JakubJaszczur/Epaper-Weather-Station-Receiver/src/myFont.h

// Created by http://oleddisplay.squix.ch/ Consider a donation
// In case of problems make sure that you are using the font file with the correct version!
const uint8_t SansSerif_bold_50Bitmaps[] PROGMEM = {

	// Bitmap Data:
	0x00, // ' '
	0xFF,0xBF,0xEF,0xFB,0xFE,0xFF,0xBF,0xEF,0xFB,0xFE,0xFF,0xBF,0xEF,0xFB,0xFE,0xFF,0xBF,0xEF,0xFB,0xFE,0xFF,0xBF,0xE7,0xF1,0xFC,0x7F,0x1F,0xC7,0xF1,0xFC,0x00,0x00,0x00,0x03,0xFE,0xFF,0xBF,0xEF,0xFB,0xFE,0xFF,0xBF,0xEF,0xFB,0xFE, // '!'
	0xFC,0x1F,0xBF,0x07,0xEF,0xC1,0xFB,0xF0,0x7E,0xFC,0x1F,0xBF,0x07,0xEF,0xC1,0xFB,0xF0,0x7E,0xFC,0x1F,0xBF,0x07,0xEF,0xC1,0xFB,0xF0,0x7E,0xFC,0x1F,0xBF,0x07,0xE0, // '"'
	0x00,0x07,0xE0,0x7E,0x00,0x00,0x7C,0x07,0xC0,0x00,0x07,0xC0,0x7C,0x00,0x00,0xFC,0x0F,0xC0,0x00,0x0F,0xC0,0xF8,0x00,0x00,0xF8,0x0F,0x80,0x00,0x0F,0x80,0xF8,0x00,0x01,0xF8,0x1F,0x80,0x00,0x1F,0x81,0xF0,0x01,0xFF,0xFF,0xFF,0xFE,0x1F,0xFF,0xFF,0xFF,0xE1,0xFF,0xFF,0xFF,0xFE,0x1F,0xFF,0xFF,0xFF,0xE1,0xFF,0xFF,0xFF,0xFE,0x00,0x3E,0x07,0xE0,0x00,0x07,0xE0,0x7E,0x00,0x00,0x7E,0x07,0xC0,0x00,0x07,0xC0,0x7C,0x00,0x00,0x7C,0x0F,0xC0,0x00,0x0F,0xC0,0xFC,0x00,0x00,0xFC,0x0F,0x80,0x0F,0xFF,0xFF,0xFF,0xF0,0xFF,0xFF,0xFF,0xFF,0x0F,0xFF,0xFF,0xFF,0xF0,0xFF,0xFF,0xFF,0xFF,0x0F,0xFF,0xFF,0xFF,0xF0,0x01,0xF0,0x1F,0x00,0x00,0x3F,0x03,0xF0,0x00,0x03,0xF0,0x3E,0x00,0x00,0x3E,0x03,0xE0,0x00,0x03,0xE0,0x3E,0x00,0x00,0x3E,0x07,0xE0,0x00,0x07,0xE0,0x7E,0x00,0x00,0x7C,0x07,0xC0,0x00,0x07,0xC0,0x7C,0x00,0x00,0x7C,0x0F,0xC0,0x00, // '#'
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
};
const GFXglyph SansSerif_bold_50Glyphs[] PROGMEM = {
// bitmapOffset, width, height, xAdvance, xOffset, yOffset
	  {     0,   1,   1,  18,    0,    0 }, // ' '
	  {     1,  10,  36,  24,    7,  -36 }, // '!'
	  {    46,  18,  14,  27,    5,  -36 }, // '"'
	  {    78,  36,  36,  43,    3,  -36 }, // '#'
	  {   240,  29,  45,  36,    3,  -38 }, // '$'
	  {   404,  48,  38,  51,    2,  -37 }, // '%'
	  {   632,  40,  38,  45,    2,  -37 }, // '&'
	  {   822,   7,  14,  16,    5,  -36 }, // '''
	  {   835,  15,  45,  24,    4,  -38 }, // '('
	  {   920,  15,  45,  24,    4,  -38 }, // ')'
	  {  1005,  25,  23,  27,    1,  -37 }, // '*'
	  {  1077,  33,  32,  43,    5,  -32 }, // '+'
	  {  1209,  12,  17,  20,    3,   -9 }, // ','
	  {  1235,  16,   7,  22,    3,  -18 }, // '-'
	  {  1249,  10,   9,  20,    5,   -9 }, // '.'
	  {  1261,  19,  41,  19,    0,  -36 }, // '/'
	  {  1359,  31,  38,  36,    2,  -37 }, // '0'
	  {  1507,  27,  36,  36,    5,  -36 }, // '1'
	  {  1629,  27,  37,  36,    4,  -37 }, // '2'
	  {  1754,  28,  38,  36,    3,  -37 }, // '3'
	  {  1887,  31,  36,  36,    2,  -36 }, // '4'
	  {  2027,  28,  37,  36,    4,  -36 }, // '5'
	  {  2157,  30,  38,  36,    3,  -37 }, // '6'
	  {  2300,  28,  36,  36,    3,  -36 }, // '7'
	  {  2426,  30,  38,  36,    3,  -37 }, // '8'
	  {  2569,  30,  38,  36,    3,  -37 }, // '9'
	  {  2712,  10,  27,  21,    6,  -27 }, // ':'
	  {  2746,  12,  35,  21,    4,  -27 }, // ';'
	  {  2799,  32,  28,  43,    5,  -30 }, // '<'
	  {  2911,  32,  17,  43,    5,  -24 }, // '='
	  {  2979,  32,  28,  43,    5,  -30 }, // '>'
	  {  3091,  23,  36,  30,    4,  -36 }, // '?'
	  {  3195,  44,  44,  51,    3,  -35 }, // '@'
	  {  3437,  39,  36,  40,    0,  -36 }, // 'A'
	  {  3613,  31,  36,  39,    5,  -36 }, // 'B'
	  {  3753,  32,  38,  38,    2,  -37 }, // 'C'
	  {  3905,  35,  36,  43,    5,  -36 }, // 'D'
	  {  4063,  27,  36,  35,    5,  -36 }, // 'E'
	  {  4185,  26,  36,  35,    5,  -36 }, // 'F'
	  {  4302,  36,  38,  42,    2,  -37 }, // 'G'
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
};
const GFXfont SansSerif_bold_50 PROGMEM = {
(uint8_t  *)SansSerif_bold_50Bitmaps,(GFXglyph *)SansSerif_bold_50Glyphs,0x20, 0x7E, 59};

// Created by http://oleddisplay.squix.ch/ Consider a donation
// In case of problems make sure that you are using the font file with the correct version!
const uint8_t SansSerif_bold_24Bitmaps[] PROGMEM = {

	// Bitmap Data:
	0x00, // ' '
	0xF7,0xBD,0xEF,0x7B,0xDE,0xF7,0xBD,0xE0,0x03,0xDE,0xF7,0x80, // '!'
	0xE7,0x73,0xB9,0xDC,0xEE,0x77,0x3B,0x9C, // '"'
	0x03,0x8E,0x00,0xE3,0x80,0x38,0xC0,0x0C,0x70,0x07,0x1C,0x1F,0xFF,0xE7,0xFF,0xF9,0xFF,0xFE,0x06,0x38,0x03,0x8E,0x00,0xE3,0x03,0xFF,0xFC,0xFF,0xFF,0x3F,0xFF,0xC1,0xC7,0x00,0x71,0x80,0x18,0xE0,0x0E,0x38,0x00, // '#'
	0x03,0x00,0x06,0x00,0x0C,0x00,0xFF,0x07,0xFF,0x8F,0xFF,0x3E,0xC6,0x79,0x80,0xF3,0x01,0xFF,0x01,0xFF,0xC1,0xFF,0xC0,0x7F,0xC0,0x6F,0x80,0xCF,0x61,0x9E,0xFF,0xFD,0xFF,0xF0,0xFF,0x80,0x18,0x00,0x30,0x00,0x60,0x00,0xC0,0x00, // '$'
	0x3E,0x00,0xC0,0x7F,0x01,0x80,0xF7,0x83,0x80,0xE3,0x83,0x00,0xE3,0x86,0x00,0xE3,0x8E,0x00,0xE3,0x8C,0x00,0xF7,0x9C,0x00,0x7F,0x18,0xF8,0x3E,0x31,0xFC,0x00,0x73,0xDE,0x00,0x63,0x8E,0x00,0xE3,0x8E,0x01,0xC3,0x8E,0x01,0x83,0x8E,0x03,0x83,0xDE,0x03,0x01,0xFC,0x06,0x00,0xF8, // '%'
	0x03,0xF0,0x01,0xFF,0x00,0x7F,0xE0,0x0F,0x04,0x01,0xE0,0x00,0x3C,0x00,0x07,0xC0,0x00,0xFC,0x00,0x3F,0xC7,0x8F,0xFC,0xF3,0xEF,0xDC,0x78,0xFF,0x8F,0x0F,0xE1,0xE0,0xFC,0x3E,0x0F,0x83,0xFF,0xF8,0x3F,0xFF,0x81,0xF9,0xF8, // '&'
	0xEE,0xEE,0xEE,0xE0, // '''
	0x1E,0x1C,0x3C,0x38,0x78,0x78,0x70,0xF0,0xF0,0xF0,0xF0,0xF0,0xF0,0xF0,0x70,0x78,0x78,0x38,0x3C,0x1C,0x1E, // '('
	0xF0,0x70,0x78,0x38,0x3C,0x3C,0x1C,0x1E,0x1E,0x1E,0x1E,0x1E,0x1E,0x1E,0x1C,0x3C,0x3C,0x38,0x78,0x70,0xF0, // ')'
	0x06,0x00,0x30,0x11,0x89,0xED,0xE3,0xFC,0x07,0x80,0xFF,0x1E,0xDE,0x46,0x20,0x30,0x01,0x80, // '*'
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
	0x03,0xFC,0x03,0xFF,0xC3,0xFF,0xF0,0xF8,0x1C,0x7C,0x01,0x1E,0x00,0x0F,0x00,0x03,0xC0,0x00,0xF0,0x3F,0xBC,0x0F,0xEF,0x03,0xFB,0xC0,0x1E,0x78,0x07,0x9F,0x01,0xE3,0xE0,0x78,0x7F,0xFE,0x0F,0xFF,0x80,0xFF,0x00, // 'G'
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
};
const GFXglyph SansSerif_bold_24Glyphs[] PROGMEM = {
// bitmapOffset, width, height, xAdvance, xOffset, yOffset
	  {     0,   1,   1,   9,    0,    0 }, // ' '
	  {     1,   5,  18,  12,    3,  -18 }, // '!'
	  {    13,   9,   7,  14,    2,  -18 }, // '"'
	  {    21,  18,  18,  21,    2,  -18 }, // '#'
	  {    62,  15,  23,  18,    1,  -19 }, // '$'
	  {   106,  24,  18,  25,    1,  -18 }, // '%'
	  {   160,  19,  18,  22,    1,  -18 }, // '&'
	  {   203,   4,   7,   8,    2,  -18 }, // '''
	  {   207,   8,  21,  12,    2,  -18 }, // '('
	  {   228,   8,  21,  12,    2,  -18 }, // ')'
	  {   249,  13,  11,  14,    0,  -18 }, // '*'
	  {   267,  16,  15,  21,    3,  -15 }, // '+'
	  {   297,   6,   8,  10,    1,   -5 }, // ','
	  {   303,   8,   3,  11,    1,   -9 }, // '-'
	  {   306,   5,   5,  10,    2,   -5 }, // '.'
	  {   310,  10,  20,  10,    0,  -18 }, // '/'
	  {   335,  15,  18,  18,    1,  -18 }, // '0'
	  {   369,  13,  18,  18,    3,  -18 }, // '1'
	  {   399,  14,  18,  18,    2,  -18 }, // '2'
	  {   431,  14,  18,  18,    1,  -18 }, // '3'
	  {   463,  16,  18,  18,    1,  -18 }, // '4'
	  {   499,  14,  18,  18,    2,  -18 }, // '5'
	  {   531,  15,  18,  18,    1,  -18 }, // '6'
	  {   565,  14,  18,  18,    2,  -18 }, // '7'
	  {   597,  15,  18,  18,    1,  -18 }, // '8'
	  {   631,  15,  18,  18,    1,  -18 }, // '9'
	  {   665,   5,  13,  11,    3,  -13 }, // ':'
	  {   674,   6,  16,  11,    2,  -13 }, // ';'
	  {   686,  16,  14,  21,    3,  -14 }, // '<'
	  {   714,  16,   9,  21,    3,  -12 }, // '='
	  {   732,  16,  14,  21,    3,  -14 }, // '>'
	  {   760,  12,  18,  15,    2,  -18 }, // '?'
	  {   787,  22,  21,  25,    2,  -18 }, // '@'
	  {   845,  19,  18,  20,    0,  -18 }, // 'A'
	  {   888,  15,  18,  19,    2,  -18 }, // 'B'
	  {   922,  16,  18,  19,    1,  -18 }, // 'C'
	  {   958,  17,  18,  21,    2,  -18 }, // 'D'
	  {   997,  13,  18,  17,    2,  -18 }, // 'E'
	  {  1027,  13,  18,  17,    2,  -18 }, // 'F'
	  {  1057,  18,  18,  21,    1,  -18 }, // 'G'
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
};
const GFXfont SansSerif_bold_24 PROGMEM = {
(uint8_t  *)SansSerif_bold_24Bitmaps,(GFXglyph *)SansSerif_bold_24Glyphs,0x20, 0x7E, 29};

const uint8_t SansSerif_plain_16Bitmaps[] PROGMEM = {

	// Bitmap Data:
	0x00, // ' '
	0xAA,0xAA,0x0A, // '!'
	0x94,0xA5,0x20, // '"'
	0x0C,0x80,0x88,0x09,0x87,0xFE,0x19,0x01,0x10,0x13,0x0F,0xFC,0x32,0x02,0x20,0x26,0x00, // '#'
	0x10,0x10,0x7C,0xD2,0x90,0x90,0x70,0x1C,0x12,0x12,0x96,0x7C,0x10,0x10, // '$'
	0x70,0x42,0x21,0x08,0x88,0x22,0x60,0x89,0x01,0xC8,0x00,0x27,0x01,0x22,0x0C,0x88,0x22,0x21,0x08,0x84,0x1C, // '%'
	0x3C,0x06,0x20,0x40,0x04,0x00,0x20,0x05,0x00,0x88,0x48,0x44,0x82,0x48,0x18,0x41,0x83,0xE4, // '&'
	0xAA, // '''
	0x33,0x10,0x88,0x42,0x10,0x84,0x10,0x86,0x18, // '('
	0xC3,0x08,0x41,0x08,0x42,0x10,0x88,0x46,0x60, // ')'
	0x10,0x10,0x92,0x7C,0x38,0xD6,0x10,0x10, // '*'
	0x08,0x02,0x00,0x80,0x20,0xFF,0x82,0x00,0x80,0x20,0x08,0x00, // '+'
	0x49,0x40, // ','
	0xF0, // '-'
	0xA0, // '.'
	0x08,0x21,0x04,0x10,0x82,0x08,0x41,0x04,0x30,0x80, // '/'
	0x3C,0x21,0x10,0x90,0x28,0x14,0x0A,0x05,0x02,0x81,0x21,0x10,0x87,0x80, // '0'
	0x70,0xD0,0x10,0x10,0x10,0x10,0x10,0x10,0x10,0x10,0x10,0xFE, // '1'
	0x78,0xC4,0x82,0x02,0x02,0x04,0x08,0x10,0x20,0x40,0x80,0xFE, // '2'
	0x7C,0x41,0x80,0x40,0x20,0x31,0xE0,0x0C,0x02,0x01,0x00,0xA0,0x8F,0x80, // '3'
	0x06,0x02,0x80,0xA0,0x48,0x22,0x10,0x84,0x22,0x08,0xFF,0x80,0x80,0x20,0x08, // '4'
	0x7E,0x20,0x10,0x08,0x07,0xC2,0x10,0x04,0x02,0x01,0x00,0xA0,0x8F,0x80, // '5'
	0x1C,0x31,0x10,0x10,0x0B,0xC6,0x12,0x05,0x02,0x81,0x40,0x90,0x87,0x80, // '6'
	0xFF,0x00,0x80,0x80,0x40,0x40,0x20,0x20,0x10,0x08,0x08,0x04,0x04,0x00, // '7'
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
	  {   408,   9,  12,  11,    1,  -12 }, // 'E'
	  {   422,   8,  12,  10,    1,  -12 }, // 'F'
	  {   434,  11,  12,  13,    1,  -12 }, // 'G'
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
};
const GFXfont SansSerif_plain_16 PROGMEM = {
(uint8_t  *)SansSerif_plain_16Bitmaps,(GFXglyph *)SansSerif_plain_16Glyphs,0x20, 0x7E, 19};
